AdrianChemicz/IoT-clock-project/clock_Pcb_schematic/clock_main_board/rev_1_1/clock_main_board_rev_1_1.sch

## KiCad design clock_Pcb_schematic/clock_main_board/rev_1_1/clock_main_board_rev_1_1.sch (2019-12-24)

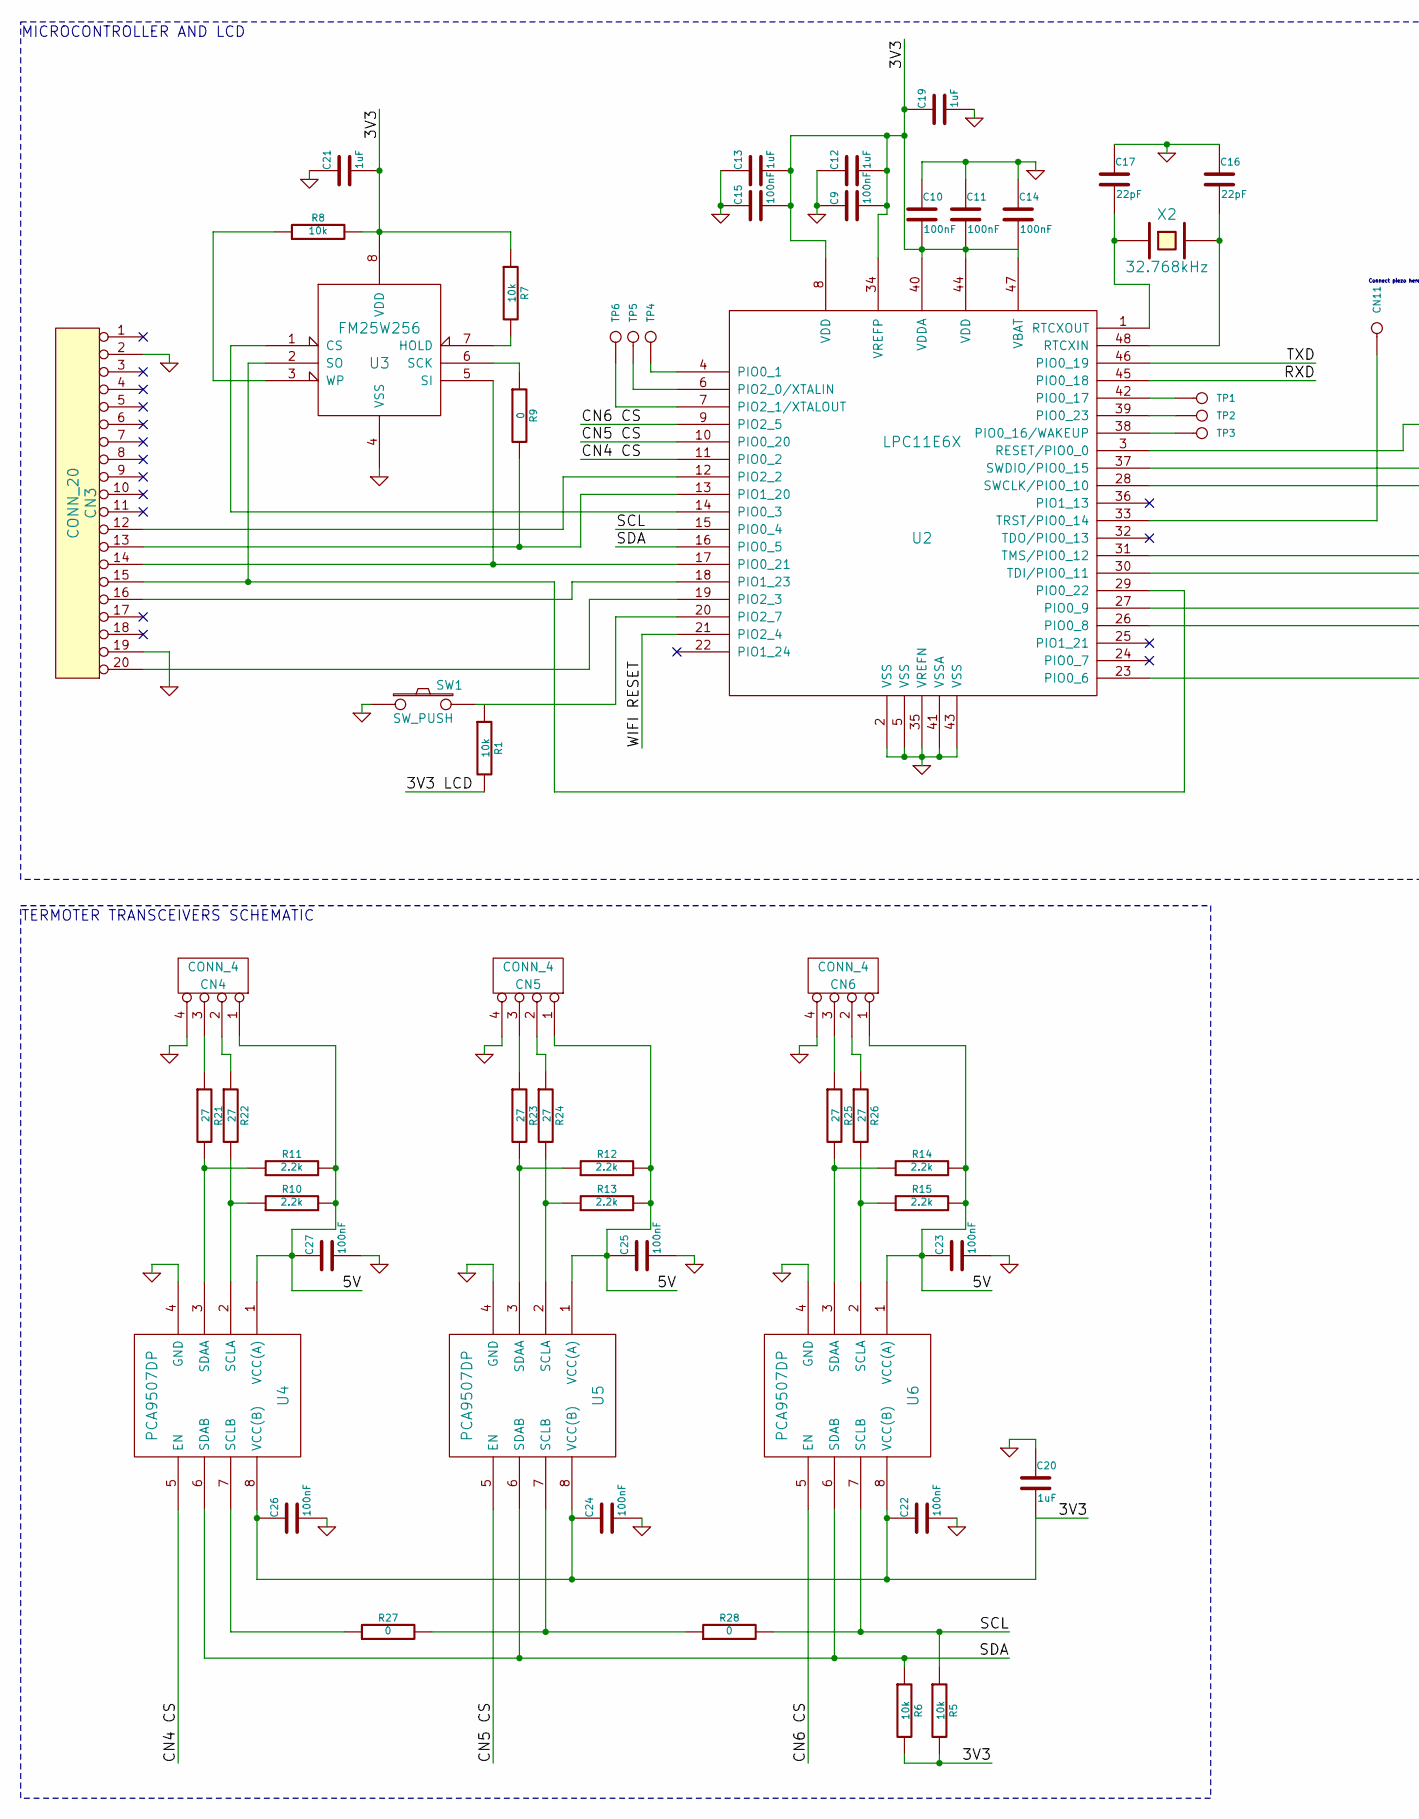
[picture p8: schematic clock_main_board_rev_1_1.sch, part in row 1, column 1]

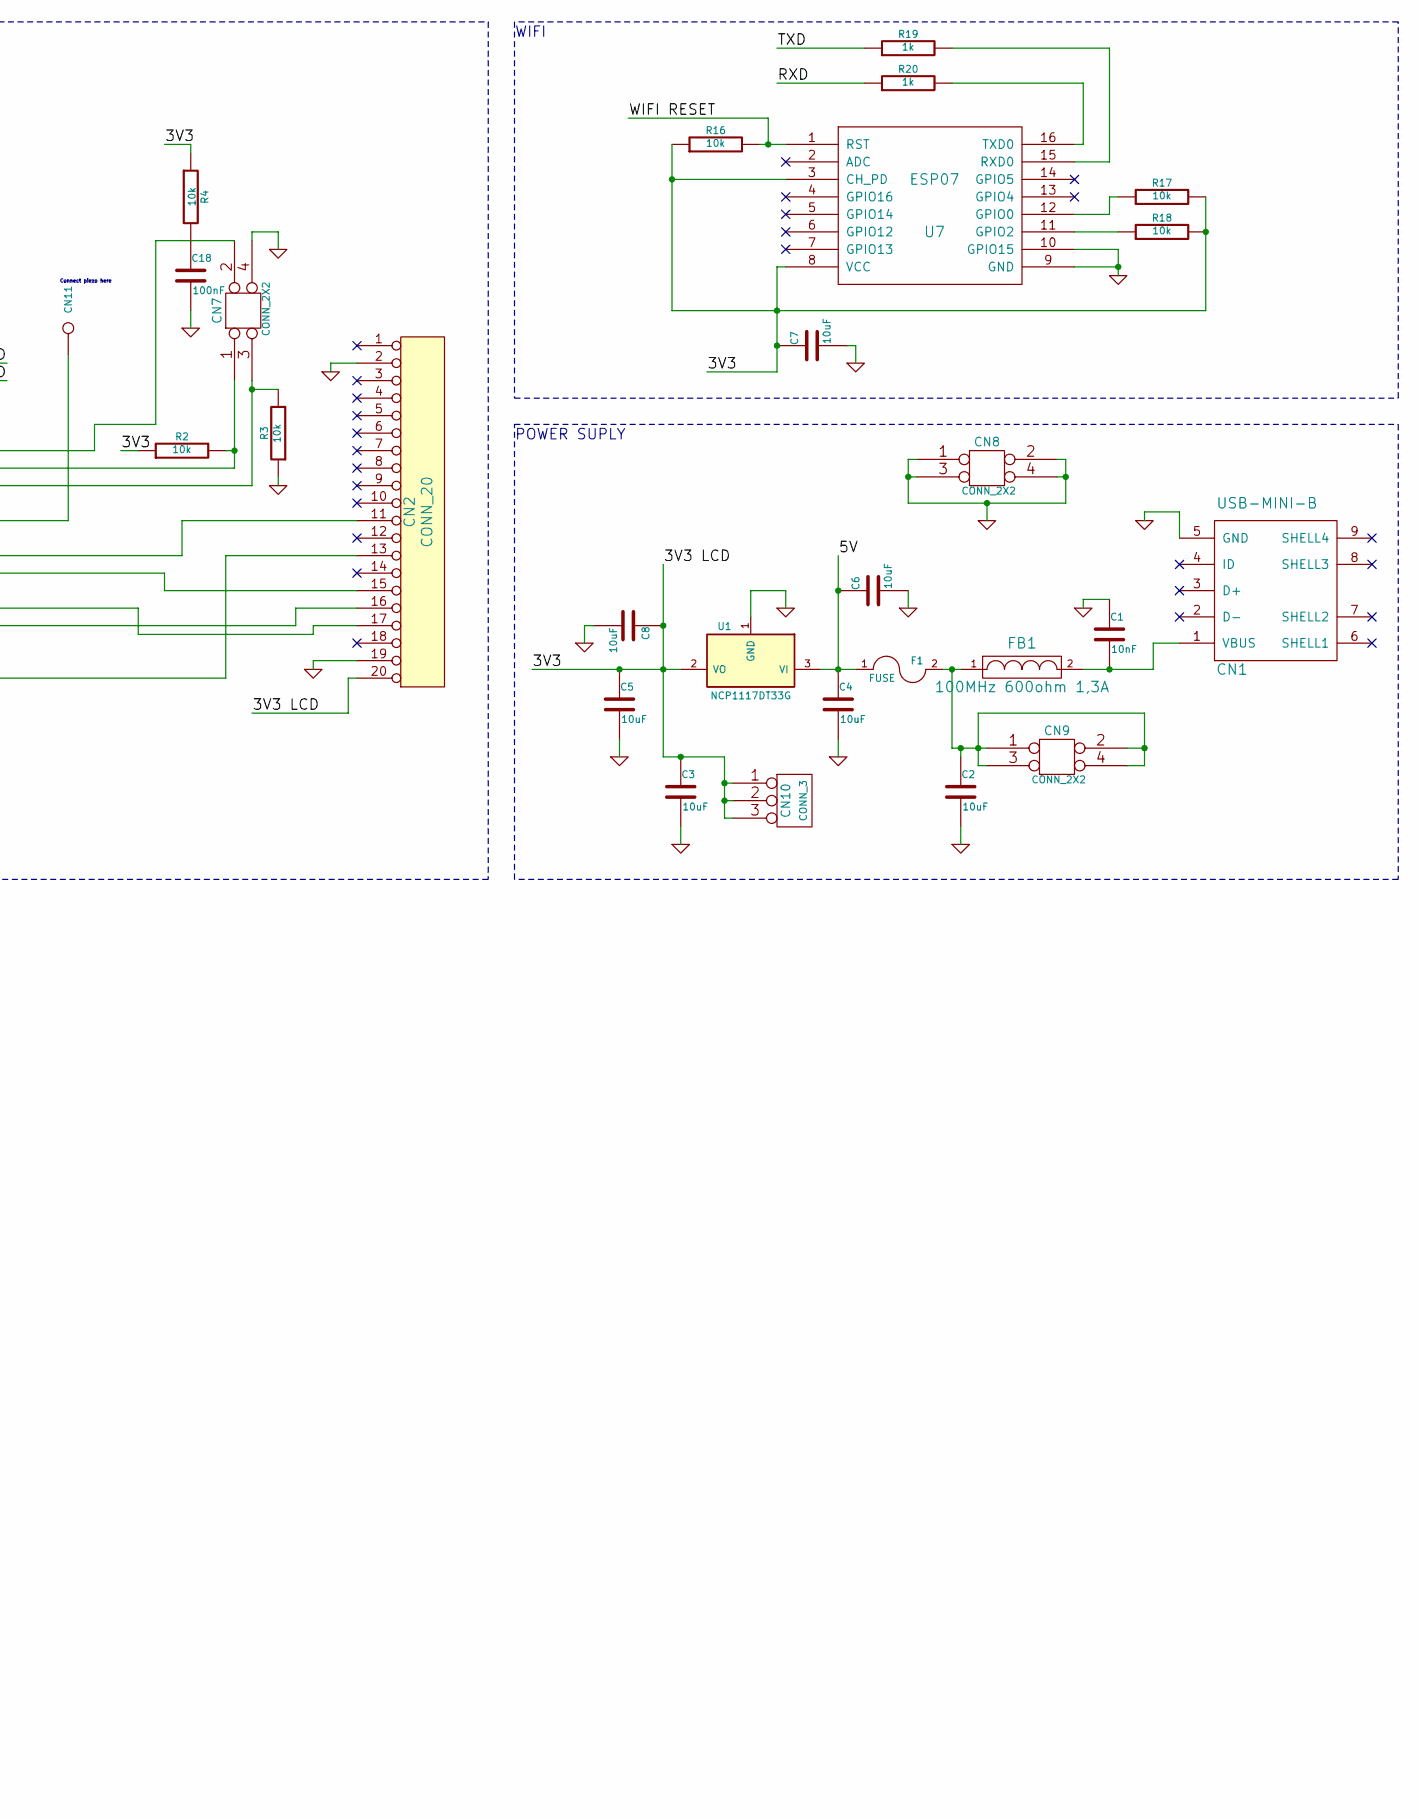
[picture p9: schematic clock_main_board_rev_1_1.sch, part in row 1, column 2]

Parts:
C1: 10nF
C2, C3, C4, C5, C6, C7, C8: 10uF
C9, C10, C11, C14, C15, C18, C22, C23, C24, C25, C26, C27: 100nF
C12, C13, C19, C20, C21: 1uF
C16, C17: 22pF
CN1: USB-MINI-B
CN2, CN3: CONN_20
CN4, CN5, CN6: CONN_4
CN7: CONN_2X2
CN8, CN9: CONN_2X2
CN10: CONN_3
CN11: CONN_1
F1: FUSE
FB1: 100MHz 600ohm 1,3A
R1, R2, R3, R4, R5, R6, R7, R8, R16, R17, R18: 10k
R9, R27, R28: 0
R10, R11, R12, R13, R14, R15: 2.2k
R19, R20: 1k
R21, R22, R23, R24, R25, R26: 27
SW1: SW_PUSH
TP1, TP2, TP3, TP4, TP5, TP6: CONN_1
U1: NCP1117DT33G
U2: LPC11E6X
U3: FM25W256
U4, U5, U6: PCA9507DP
U7: ESP07
X2: 32.768kHz

Connections:
3V3: C3.1, C5.1, C7.1, C8.1, C9.2, C10.2, C11.2, C12.2, C13.2, C14.2, C15.2, C19.1, C20.2, C21.2, C22.1, C24.1, C26.1, CN2.20, CN10.1, CN10.2 (PM), CN10.3, R1.2, R2.1, R4.1, R5.2, R6.2, R7.1, R8.2, R16.1, R17.2, R18.2, U1.2 (VO), U2.8 (VDD), U2.34 (VREFP), U2.40 (VDDA), U2.44 (VDD), U2.47 (VBAT), U3.8 (VDD), U4.8 (VCC(B)), U5.8 (VCC(B)), U6.8 (VCC(B)), U7.3 (CH_PD), U7.8 (VCC)
5V: C4.1, C6.1, C23.1, C25.1, C27.1, CN4.1, CN5.1, CN6.1, F1.1, R10.2, R11.2, R12.2, R13.2, R14.2, R15.2, U1.3 (VI), U4.1 (VCC(A)), U5.1 (VCC(A)), U6.1 (VCC(A))
CN4 CS: U2.11 (PIO0_2), U4.5 (EN)
CN5 CS: U2.10 (PIO0_20), U5.5 (EN)
CN6 CS: U2.9 (PIO2_5), U6.5 (EN)
GND: C1.1, C2.2, C3.2, C4.2, C5.2, C6.2, C7.2, C8.2, C9.1, C10.1, C11.1, C12.1, C13.1, C14.1, C15.1, C16.1, C17.1, C18.2, C19.2, C20.1, C21.1, C22.2, C23.2, C24.2, C25.2, C26.2, C27.2, CN1.5 (GND), CN2.2, CN2.19, CN3.2, CN3.19, CN4.4, CN5.4, CN6.4, CN7.4, CN8.1, CN8.2, CN8.3, CN8.4, R3.1, SW1.1, U1.1 (GND), U2.2 (VSS), U2.5 (VSS), U2.35 (VREFN), U2.41 (VSSA), U2.43 (VSS), U3.4 (VSS), U4.4 (GND), U5.4 (GND), U6.4 (GND), U7.9 (GND), U7.10 (GPIO15)
unnamed: C1.2, CN1.1 (VBUS), FB1.2
unnamed: C2.1, CN9.1, CN9.2, CN9.3, CN9.4, F1.2, FB1.1
unnamed: C16.2, U2.48 (RTCXIN), X2.2
unnamed: C17.2, U2.1 (RTCXOUT), X2.1
unnamed: C18.1, R4.2
unnamed: CN2.11, U2.31 (TMS/PIO0_12)
unnamed: CN2.13, U2.23 (PIO0_6)
unnamed: CN2.15, U2.30 (TDI/PIO0_11)
unnamed: CN2.16, U2.26 (PIO0_8)
unnamed: CN2.17, U2.27 (PIO0_9)
unnamed: CN3.12, U2.12 (PIO2_2)
unnamed: CN3.13, R9.2, U2.13 (PIO1_20)
unnamed: CN3.14, U2.17 (PIO0_21), U3.5 (SI)
unnamed: CN3.15, U2.29 (PIO0_22), U3.2 (SO)
unnamed: CN3.16, U2.18 (PIO1_23)
unnamed: CN3.20, U2.19 (PIO2_3)
unnamed: CN4.2, R22.1
unnamed: CN4.3, R21.1
unnamed: CN5.2, R24.1
unnamed: CN5.3, R23.1
unnamed: CN6.2, R26.1
unnamed: CN6.3, R25.1
unnamed: CN7.1, R2.2, U2.37 (SWDIO/PIO0_15)
unnamed: CN7.2, U2.3 (RESET/PIO0_0)
unnamed: CN7.3, R3.2, U2.28 (SWCLK/PIO0_10)
unnamed: CN11.1, U2.33 (TRST/PIO0_14)
unnamed: R7.2, U3.7 (HOLD)
unnamed: R8.1, U3.3 (WP)
unnamed: R9.1, U3.6 (SCK)
unnamed: R10.1, R22.2, U4.2 (SCLA)
unnamed: R11.1, R21.2, U4.3 (SDAA)
unnamed: R12.1, R23.2, U5.3 (SDAA)
unnamed: R13.1, R24.2, U5.2 (SCLA)
unnamed: R14.1, R25.2, U6.3 (SDAA)
unnamed: R15.1, R26.2, U6.2 (SCLA)
unnamed: R17.1, U7.12 (GPIO0)
unnamed: R18.1, U7.11 (GPIO2)
unnamed: R19.2, U7.15 (RXD0)
unnamed: R20.2, U7.16 (TXD0)
unnamed: R27.1, U4.7 (SCLB)
unnamed: R27.2, R28.1, U5.7 (SCLB)
unnamed: SW1.2, U2.20 (PIO2_7)
unnamed: TP1.1, U2.42 (PIO0_17)
unnamed: TP2.1, U2.39 (PIO0_23)
unnamed: TP3.1, U2.38 (PIO0_16/WAKEUP)
unnamed: TP4.1, U2.4 (PIO0_1)
unnamed: TP5.1, U2.6 (PIO2_0/XTALIN)
unnamed: TP6.1, U2.7 (PIO2_1/XTALOUT)
unnamed: U2.14 (PIO0_3), U3.1 (CS)
RXD: R20.1, U2.45 (PIO0_18)
SCL: R5.1, R28.2, U2.15 (PIO0_4), U6.7 (SCLB)
SDA: R6.1, U2.16 (PIO0_5), U4.6 (SDAB), U5.6 (SDAB), U6.6 (SDAB)
TXD: R19.1, U2.46 (PIO0_19)
WIFI RESET: R16.2, U2.21 (PIO2_4), U7.1 (RST)

Notes on the sheet:
POWER SUPLY
WIFI
Connect piezo here
MICROCONTROLLER AND LCD
TERMOTER TRANSCEIVERS SCHEMATIC
