AdrianChemicz/IoT-clock-project/clock_Pcb_schematic/clock_temperature_board/rev_1_0/clock_temperature_board.sch

## KiCad design clock_Pcb_schematic/clock_temperature_board/rev_1_0/clock_temperature_board.sch (2019-12-24)

Schematic: clock_temperature_board.sch

Parts:
C1: 4,7uF
C2, C5, C6: 100nF
C3, C4: 1uF
CN1: CONN_4
R1, R2: 27
R3, R4: 47k
R5, R6: 10k
U1: MCP1700T-3302E
U2: PCA9507DP
U3: SI7021-A20
