AdrianChemicz/IoT-clock-project/clock_firmware/src/FRAM_Driver.c

/*
 * Copyright (c) 2018, 2019, Adrian Chemicz
 * All rights reserved.
 *
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
 * THIS SOFTWARE IS PROVIDED BY THE COPYRIGHT HOLDERS AND CONTRIBUTORS "AS IS" AND
 * ANY EXPRESS OR IMPLIED WARRANTIES, INCLUDING, BUT NOT LIMITED TO, THE IMPLIED
 * WARRANTIES OF MERCHANTABILITY AND FITNESS FOR A PARTICULAR PURPOSE ARE
 * DISCLAIMED. IN NO EVENT SHALL COPYRIGHT HOLDER BE LIABLE FOR ANY
 * DIRECT, INDIRECT, INCIDENTAL, SPECIAL, EXEMPLARY, OR CONSEQUENTIAL DAMAGES
 * (INCLUDING, BUT NOT LIMITED TO, PROCUREMENT OF SUBSTITUTE GOODS OR SERVICES;
 * LOSS OF USE, DATA, OR PROFITS; OR BUSINESS INTERRUPTION) HOWEVER CAUSED AND
 * ON ANY THEORY OF LIABILITY, WHETHER IN CONTRACT, STRICT LIABILITY, OR TORT
 * (INCLUDING NEGLIGENCE OR OTHERWISE) ARISING IN ANY WAY OUT OF THE USE OF THIS
 * SOFTWARE, EVEN IF ADVISED OF THE POSSIBILITY OF SUCH DAMAGE.
 */

#include "FRAM_Driver.h"
#include "GPIO_Driver.h"
#include "SPI_Driver.h"

static uint8_t portNumber;
static OperationType Operation;
static uint8_t* memoryPointer;
static uint16_t numOfDataToCopy;
static uint16_t numOfDataCopied;
static uint16_t dataAddressWrite;

static inline void FRAM_ClearSpiBuffer()
{
	for(uint16_t i = 0;i<SPI_BUFFER_SIZE;i++)
		(void)SPI_ReadByteFromTrasmitter(portNumber);
}

void FRAM_Init(uint8_t port)
{
	portNumber = port;
	Operation = NONE;
	memoryPointer = 0;

	//configure GPIO
	GPIO_Direction(FRAM_PIN_CS_GPIO_PORT, FRAM_PIN_CS_GPIO_PIN, GPIO_DIR_OUTPUT);

	//set pin in high state
	GPIO_SetState(FRAM_PIN_CS_GPIO_PORT, FRAM_PIN_CS_GPIO_PIN, true);

	FRAM_ClearSpiBuffer();
}

bool FRAM_Process(void)
{
	bool returnState = false;

	if(SPI_CheckBusyFlag(portNumber))
		return false;

	switch(Operation)
	{
	case PREPARE_MEMORY_WRITE:
		//set pin in high state after send write enable opcode
		GPIO_SetState(FRAM_PIN_CS_GPIO_PORT, FRAM_PIN_CS_GPIO_PIN, true);

		for(uint16_t i = 0;i<16;i++)
			asm("nop");

		//set pin in low state
		GPIO_SetState(FRAM_PIN_CS_GPIO_PORT, FRAM_PIN_CS_GPIO_PIN, false);

		//send opcode with write command
		SPI_PutByteToTransmitter(portNumber, OPCODE_WRITE);

		//send address
		SPI_PutByteToTransmitter(portNumber, (uint8_t)(dataAddressWrite>>8));
		SPI_PutByteToTransmitter(portNumber, (uint8_t)(dataAddressWrite & 0xFF));

		Operation = MEMORY_WRITE;
		returnState = false;
		break;

	case MEMORY_WRITE:
		//check finish transaction statement
		if(numOfDataCopied >= numOfDataToCopy)
		{
			Operation = FINALIZE_MEMORY_TRANSACTION;
		}

		for(uint16_t i = 0;(i < SPI_BUFFER_SIZE) && (numOfDataCopied < numOfDataToCopy);i++, numOfDataCopied++)
		{
			SPI_PutByteToTransmitter(portNumber, memoryPointer[numOfDataCopied]);
		}
		returnState = false;
		break;

	case PREPARE_MEMORY_READ:
		FRAM_ClearSpiBuffer();

		Operation = MEMORY_READ;
		returnState =  false;
		break;

	case MEMORY_READ:
		;
		static uint16_t readCounter = 0;

		if(numOfDataCopied == 0)
		{
			readCounter = 0;
			FRAM_ClearSpiBuffer();
		}
		else
		{
			//copy RX data to memory buffer
			for (; SPI_CheckRxFifoNotEmpty(portNumber);readCounter++)
			{
				memoryPointer[readCounter] = SPI_ReadByteFromTrasmitter(portNumber);
			}
		}

		for(uint16_t i = 0;(i < SPI_BUFFER_SIZE) && (numOfDataCopied < numOfDataToCopy);i++, numOfDataCopied++)
			SPI_PutByteToTransmitter(portNumber, 0xFF);

		//check finish transaction statement
		if(readCounter >= numOfDataToCopy)
			Operation = FINALIZE_MEMORY_TRANSACTION;
		returnState = false;
		break;

	case FINALIZE_MEMORY_TRANSACTION:
		//set pin in high state
		GPIO_SetState(FRAM_PIN_CS_GPIO_PORT, FRAM_PIN_CS_GPIO_PIN, true);

		FRAM_ClearSpiBuffer();

		Operation = NONE;

		returnState = true;
		break;

	case NONE:
	default:
		break;
	}
	return returnState;
}

void FRAM_Write(uint16_t dataAddress, uint16_t numOfBytes, uint8_t* writeBufferPointer)
{
	//initialize global variable
	numOfDataCopied = 0;
	memoryPointer = writeBufferPointer;
	numOfDataToCopy = numOfBytes;
	Operation = PREPARE_MEMORY_WRITE;
	dataAddressWrite = dataAddress;

	//set pin in low state
	GPIO_SetState(FRAM_PIN_CS_GPIO_PORT, FRAM_PIN_CS_GPIO_PIN, false);

	//send opcode with write enable command
	SPI_PutByteToTransmitter(portNumber, OPCODE_WREN);
}

void FRAM_Read(uint16_t dataAddress, uint16_t numOfBytes, uint8_t* readBufferPointer)
{
	//initialize global variable
	numOfDataCopied = 0;
	memoryPointer = readBufferPointer;
	numOfDataToCopy = numOfBytes;
	Operation = PREPARE_MEMORY_READ;

	//set pin in low state
	GPIO_SetState(FRAM_PIN_CS_GPIO_PORT, FRAM_PIN_CS_GPIO_PIN, false);

	//send opcode with write command
	SPI_PutByteToTransmitter(portNumber, OPCODE_READ);

	//send address
	SPI_PutByteToTransmitter(portNumber, (uint8_t)(dataAddress>>8));
	SPI_PutByteToTransmitter(portNumber, (uint8_t)(dataAddress & 0xFF));
}
